Ikyua/ECOlibrium2024/outdoor module wiring 2.kicad_sch

## KiCad design outdoor module wiring 2.kicad_sch (2023-08-17)

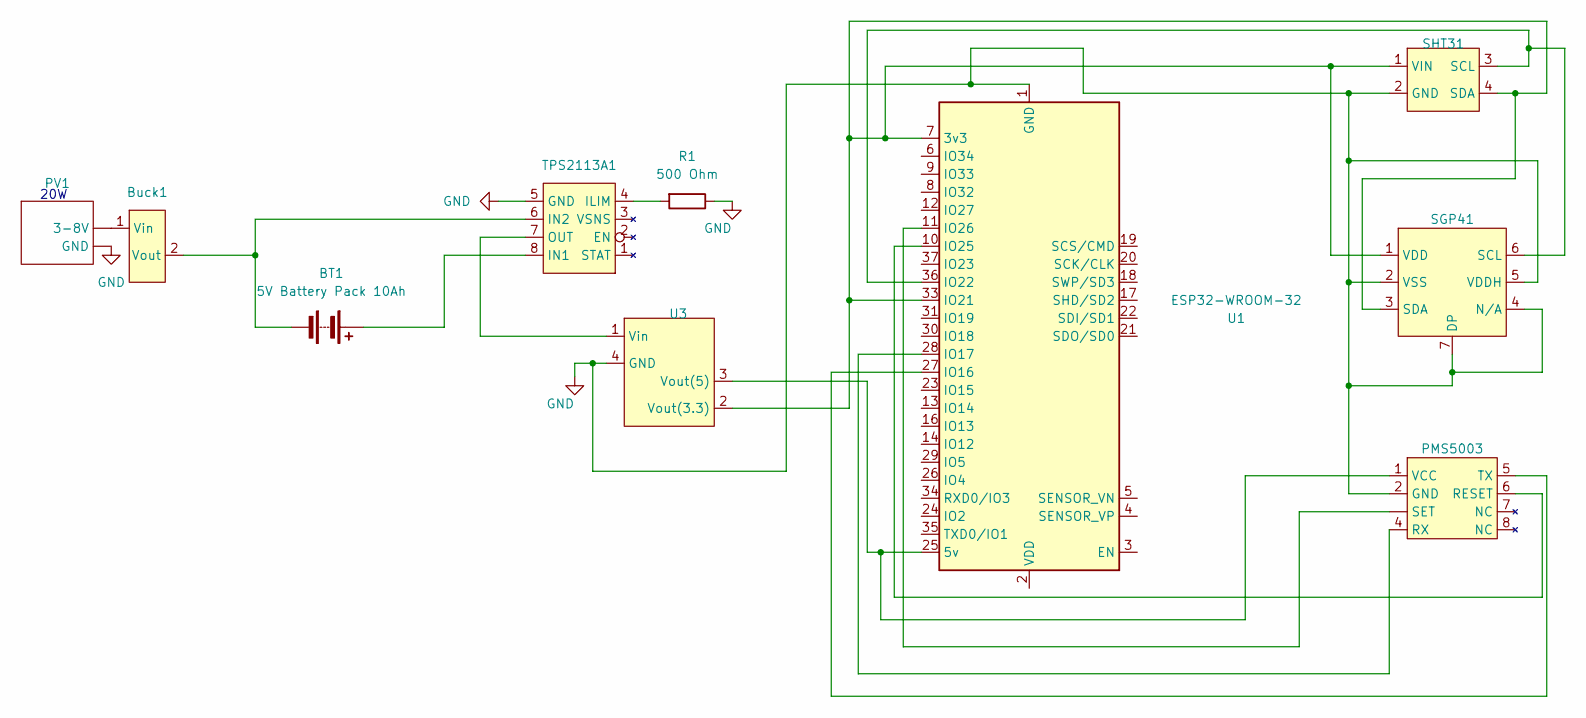
[picture p9: schematic outdoor module wiring 2.kicad_sch]

Parts:
BT1: 5V Battery Pack 10Ah
Buck1: (no value)
PMS5003: (no value)
PV1: (no value)
R1: 500 Ohm
SGP41: (no value)
SHT31: (no value)
TPS2113A1: (no value)
U1: ESP32-WROOM-32
U3: (no value)

Connections:
GND: PMS5003.2 (GND), PV1., R1.1, SGP41.2 (VSS), SGP41.4 (N/A), SGP41.5 (VDDH), SGP41.7 (DP), SHT31.2 (GND), TPS2113A1.5 (GND), U1.1 (GND), U1.15 (GND), U1.38 (GND), U1.39 (GND), U3.4 (GND)
unnamed: BT1.1 (+), TPS2113A1.8 (IN1)
unnamed: BT1.2 (-), Buck1.2 (Vout), TPS2113A1.6 (IN2)
unnamed: Buck1.1 (Vin), PV1.
unnamed: PMS5003.1 (VCC), U1.25 (5v), U3.3 (Vout(5))
unnamed: PMS5003.4 (RX), U1.28 (IO17)
unnamed: PMS5003.5 (TX), U1.27 (IO16)
unnamed: PMS5003.6 (RESET), U1.10 (IO25)
unnamed: PMS5003. (SET), U1.11 (IO26)
unnamed: R1.2, TPS2113A1.4 (ILIM)
unnamed: SGP41.1 (VDD), SGP41.3 (SDA), SHT31.1 (VIN), SHT31.4 (SDA), U1.7 (3v3), U1.33 (IO21), U3.2 (Vout(3.3))
unnamed: SGP41.6 (SCL), SHT31.3 (SCL), U1.36 (IO22)
unnamed: TPS2113A1.7 (OUT), U3.1 (Vin)

Notes on the sheet:
20W
