Ikyua/ECOlibrium2024/outdoor module wiring.kicad_sch

## KiCad design outdoor module wiring.kicad_sch (2023-08-17)

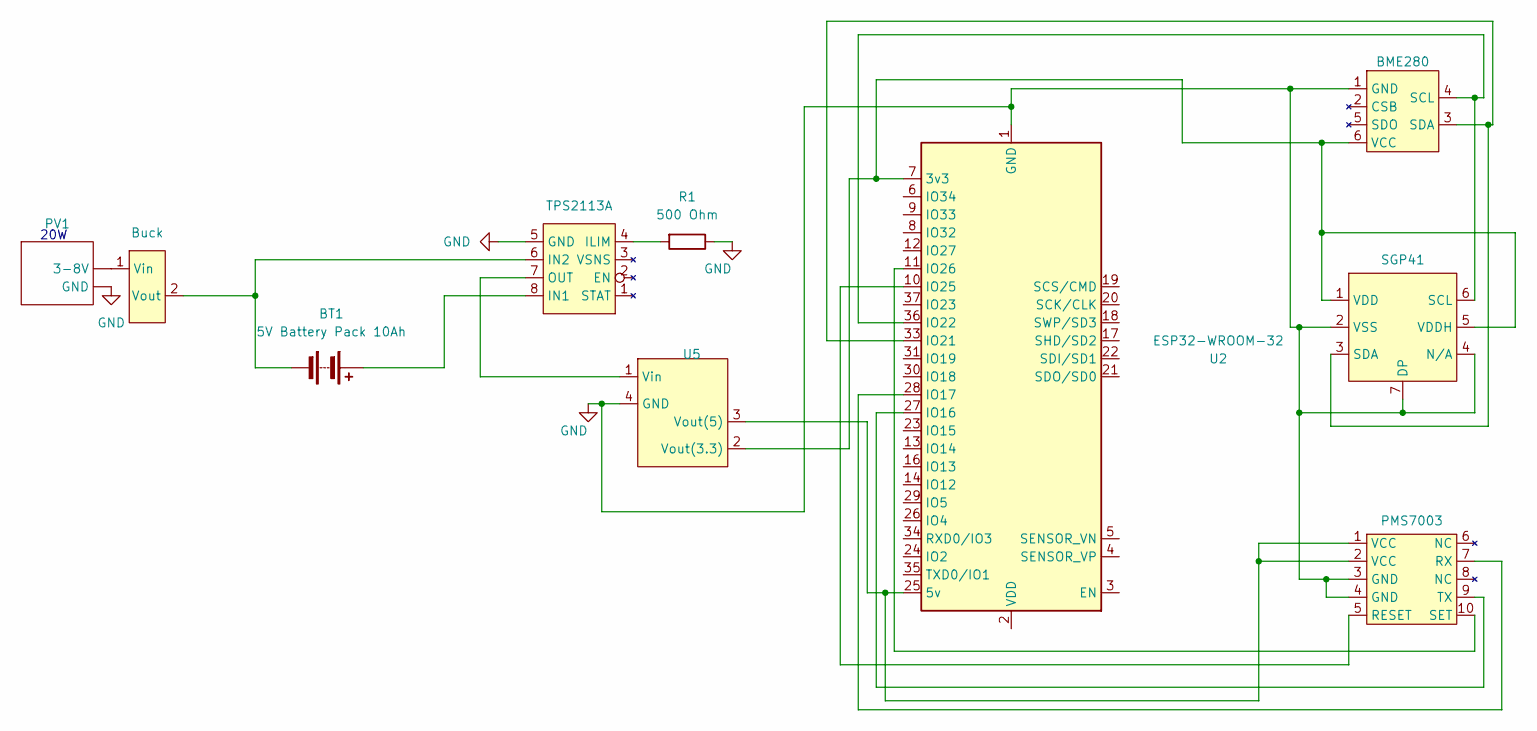
[picture p10: schematic outdoor module wiring.kicad_sch]

Parts:
BME280: (no value)
BT1: 5V Battery Pack 10Ah
Buck: (no value)
PMS7003: (no value)
PV1: (no value)
R1: 500 Ohm
SGP41: (no value)
TPS2113A: (no value)
U2: ESP32-WROOM-32
U5: (no value)

Connections:
GND: BME280.1 (GND), PMS7003.3 (GND), PMS7003.4 (GND), PV1., R1.1, SGP41.2 (VSS), SGP41.4 (N/A), SGP41.7 (DP), TPS2113A.5 (GND), U2.1 (GND), U2.15 (GND), U2.38 (GND), U2.39 (GND), U5.4 (GND)
unnamed: BME280.3 (SDA), SGP41.3 (SDA), U2.33 (IO21)
unnamed: BME280.4 (SCL), SGP41.6 (SCL), U2.36 (IO22)
unnamed: BME280.6 (VCC), SGP41.1 (VDD), SGP41.5 (VDDH), U2.7 (3v3), U5.2 (Vout(3.3))
unnamed: BT1.1 (+), TPS2113A.8 (IN1)
unnamed: BT1.2 (-), Buck.2 (Vout), TPS2113A.6 (IN2)
unnamed: Buck.1 (Vin), PV1.
unnamed: PMS7003.1 (VCC), PMS7003.2 (VCC), U2.25 (5v), U5.3 (Vout(5))
unnamed: PMS7003.5 (RESET), U2.10 (IO25)
unnamed: PMS7003.7 (RX), U2.28 (IO17)
unnamed: PMS7003.9 (TX), U2.27 (IO16)
unnamed: PMS7003.10 (SET), U2.11 (IO26)
unnamed: R1.2, TPS2113A.4 (ILIM)
unnamed: TPS2113A.7 (OUT), U5.1 (Vin)

Notes on the sheet:
20W
