Ikyua/ECOlibrium2024/Power Structure/Loisaida Power Schematic.kicad_sch

## KiCad design Power Structure/Loisaida Power Schematic.kicad_sch (2023-08-11)

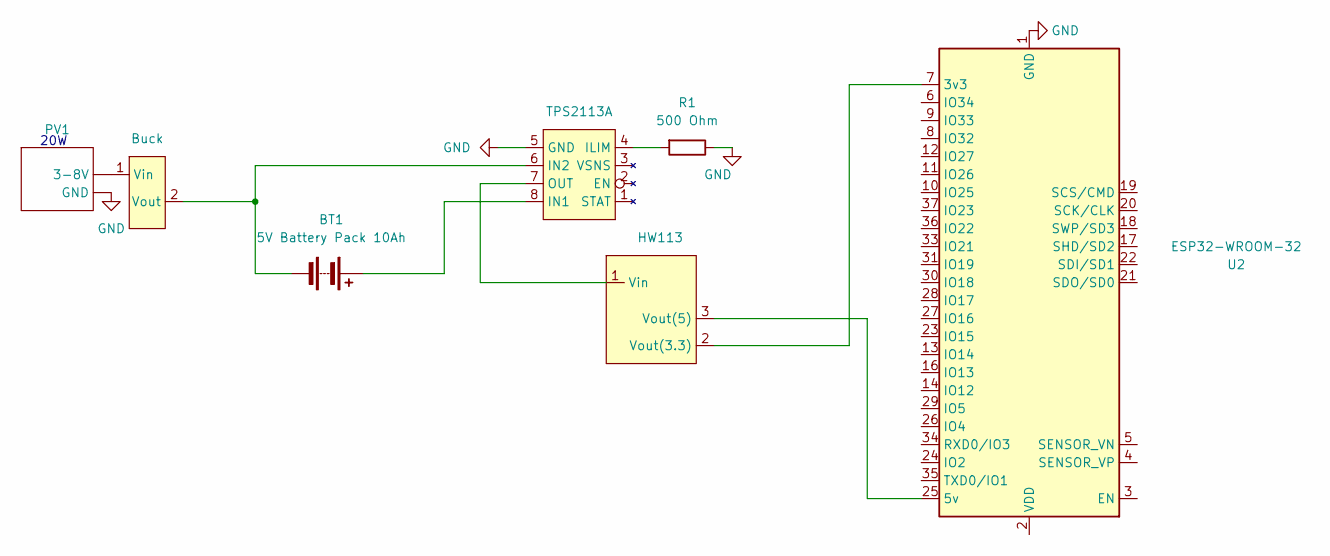
[picture p11: schematic Loisaida Power Schematic.kicad_sch]

Parts:
BT1: 5V Battery Pack 10Ah
Buck: (no value)
HW113: (no value)
PV1: (no value)
R1: 500 Ohm
TPS2113A: (no value)
U2: ESP32-WROOM-32

Connections:
GND: PV1., R1.1, TPS2113A.5 (GND), U2.1 (GND), U2.15 (GND), U2.38 (GND), U2.39 (GND)
unnamed: BT1.1 (+), TPS2113A.8 (IN1)
unnamed: BT1.2 (-), Buck.2 (Vout), TPS2113A.6 (IN2)
unnamed: Buck.1 (Vin), PV1.
unnamed: HW113.1 (Vin), TPS2113A.7 (OUT)
unnamed: HW113.2 (Vout(3.3)), U2.7 (3v3)
unnamed: HW113.3 (Vout(5)), U2.25 (5v)
unnamed: R1.2, TPS2113A.4 (ILIM)

Notes on the sheet:
20W
