Ikyua/ECOlibrium2024/GPSHardwareConfig.ino

#include <TinyGPS++.h>
//#include <SoftwareSerial.h>

HardwareSerial GPSuart(2);
HardwareSerial PMSuart(1);
TinyGPSPlus gps;

void setup()
{
  GPSuart.begin(9600, SERIAL_8N1, 17, 16);
  PMSuart.begin(9600, SERIAL_8N1, 1, 3);
  Serial.begin(9600);
  
  Serial.println(F("DeviceExample.ino"));
  Serial.println(F("A simple demonstration of TinyGPS++ with an attached GPS module"));
  Serial.print(F("Testing TinyGPS++ library v. ")); Serial.println(TinyGPSPlus::libraryVersion());
  Serial.println(F("by Mikal Hart"));
  Serial.println();
}

struct pms5003data {
  uint16_t framelen;
  uint16_t pm10_standard, pm25_standard, pm100_standard;
  uint16_t pm10_env, pm25_env, pm100_env;
  uint16_t particles_03um, particles_05um, particles_10um, particles_25um, particles_50um, particles_100um;
  uint16_t unused;
  uint16_t checksum;
};

struct pms5003data data;

void loop()
{
  // This sketch displays information every time a new sentence is correctly encoded.
  while (uart.available() > 0)
    if (gps.encode(uart.read()))
      displayInfo();

  if (millis() > 5000 && gps.charsProcessed() < 10)
  {
    Serial.println(F("No GPS detected: check wiring."));
    while(true);
  }
  if (readPMSdata(&Serial1)) {
    // reading data was successful!
    Serial.println();
    Serial.println("---------------------------------------");
    Serial.println("Concentration Units (standard)");
    Serial.print("PM 1.0: "); Serial.print(data.pm10_standard);
    Serial.print("\t\tPM 2.5: "); Serial.print(data.pm25_standard);
    Serial.print("\t\tPM 10: "); Serial.println(data.pm100_standard);
    Serial.println("---------------------------------------");
    Serial.println("Concentration Units (environmental)");
    Serial.print("PM 1.0: "); Serial.print(data.pm10_env);
    Serial.print("\t\tPM 2.5: "); Serial.print(data.pm25_env);
    Serial.print("\t\tPM 10: "); Serial.println(data.pm100_env);
    Serial.println("---------------------------------------");
    Serial.print("Particles > 0.3um / 0.1L air:"); Serial.println(data.particles_03um);
    Serial.print("Particles > 0.5um / 0.1L air:"); Serial.println(data.particles_05um);
    Serial.print("Particles > 1.0um / 0.1L air:"); Serial.println(data.particles_10um);
    Serial.print("Particles > 2.5um / 0.1L air:"); Serial.println(data.particles_25um);
    Serial.print("Particles > 5.0um / 0.1L air:"); Serial.println(data.particles_50um);
    Serial.print("Particles > 10.0 um / 0.1L air:"); Serial.println(data.particles_100um);
    Serial.println("---------------------------------------");
  }
}

void displayInfo()
{
  Serial.print(F("Location: ")); 
  if (gps.location.isValid())
  {
    Serial.print(gps.location.lat(), 6);
    Serial.print(F(","));
    Serial.print(gps.location.lng(), 6);
  }
  else
  {
    Serial.print(F("INVALID"));
  }

  Serial.print(F("  Date/Time: "));
  if (gps.date.isValid())
  {
    Serial.print(gps.date.month());
    Serial.print(F("/"));
    Serial.print(gps.date.day());
    Serial.print(F("/"));
    Serial.print(gps.date.year());
  }
  else
  {
    Serial.print(F("INVALID"));
  }

  Serial.print(F(" "));
  if (gps.time.isValid())
  {
    if (gps.time.hour() < 10) Serial.print(F("0"));
    Serial.print(gps.time.hour());
    Serial.print(F(":"));
    if (gps.time.minute() < 10) Serial.print(F("0"));
    Serial.print(gps.time.minute());
    Serial.print(F(":"));
    if (gps.time.second() < 10) Serial.print(F("0"));
    Serial.print(gps.time.second());
    Serial.print(F("."));
    if (gps.time.centisecond() < 10) Serial.print(F("0"));
    Serial.print(gps.time.centisecond());
  }
  else
  {
    Serial.print(F("INVALID"));
  }

  Serial.println();
}

boolean readPMSdata(Stream *s) {
  if (! s->available()) {
    return false;
  }

  // Read a byte at a time until we get to the special '0x42' start-byte
  if (s->peek() != 0x42) {
    s->read();
    return false;
  }

  // Now read all 32 bytes
  if (s->available() < 32) {
    return false;
  }

  uint8_t buffer[32];
  uint16_t sum = 0;
  s->readBytes(buffer, 32);

  // get checksum ready
  for (uint8_t i = 0; i < 30; i++) {
    sum += buffer[i];
  }

  /* debugging
    for (uint8_t i=2; i<32; i++) {
    Serial.print("0x"); Serial.print(buffer[i], HEX); Serial.print(", ");
    }
    Serial.println();
  */

  // The data comes in endian'd, this solves it so it works on all platforms
  uint16_t buffer_u16[15];
  for (uint8_t i = 0; i < 15; i++) {
    buffer_u16[i] = buffer[2 + i * 2 + 1];
    buffer_u16[i] += (buffer[2 + i * 2] << 8);
  }

  // put it into a nice struct :)
  memcpy((void *)&data, (void *)buffer_u16, 30);

  if (sum != data.checksum) {
    Serial.println("Checksum failure");
    return false;
  }
  // success!
  return true;

}
